vfalendysh/AuRA-1.3/STL/Spacer 12mm - 2x.stl

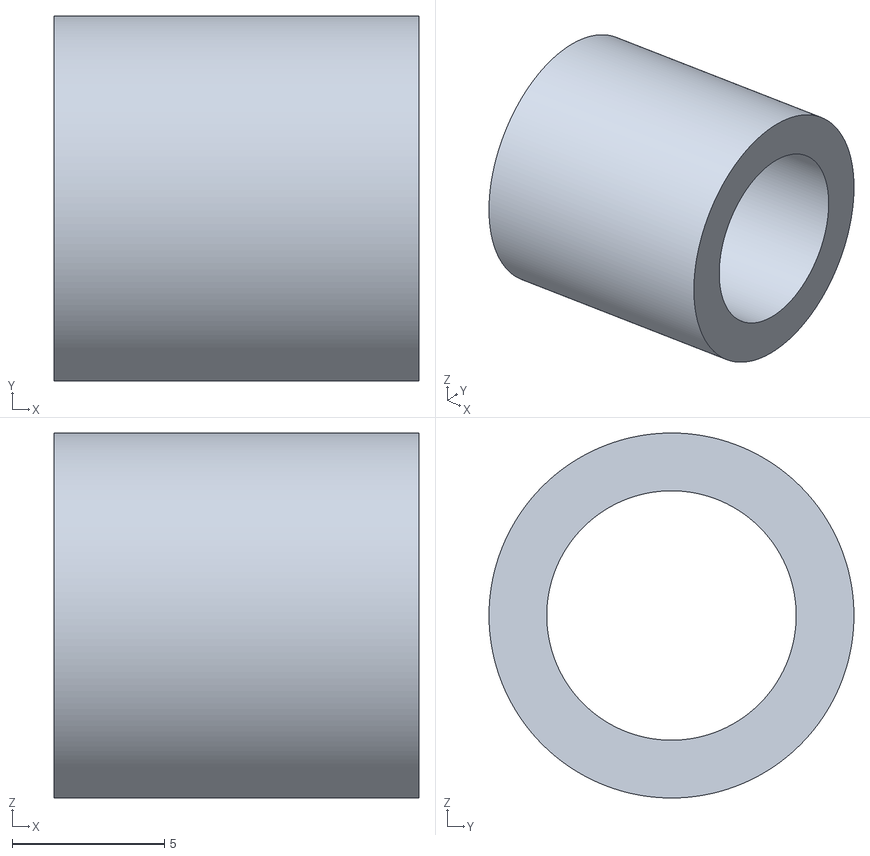
[picture p15: CAD file, 2024-05-07]
STL/Spacer 12mm - 2x.stl
12.0 x 12.0 x 12.0
