vfalendysh/AuRA-1.3/STL/Roller Jobo - 2x.stl

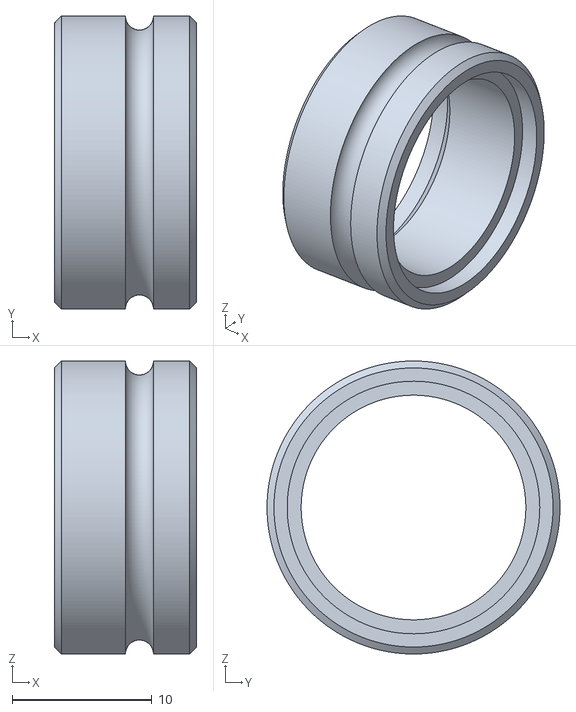
[picture p16: CAD file, 2024-05-07]
STL/Roller Jobo - 2x.stl
10.2 x 21.0 x 21.0
