vfalendysh/AuRA-1.3/STL/Spacer 08mm - 2x.stl

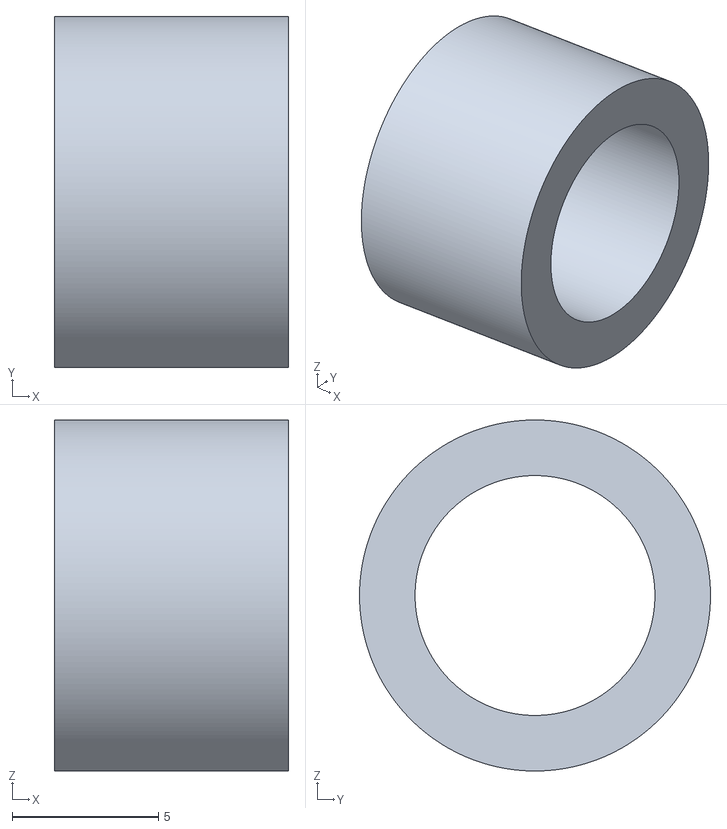
[picture p17: CAD file, 2024-05-07]
STL/Spacer 08mm - 2x.stl
8.00 x 12.0 x 12.0
