vfalendysh/AuRA-1.3/STL/Roller Flat - 6x.stl

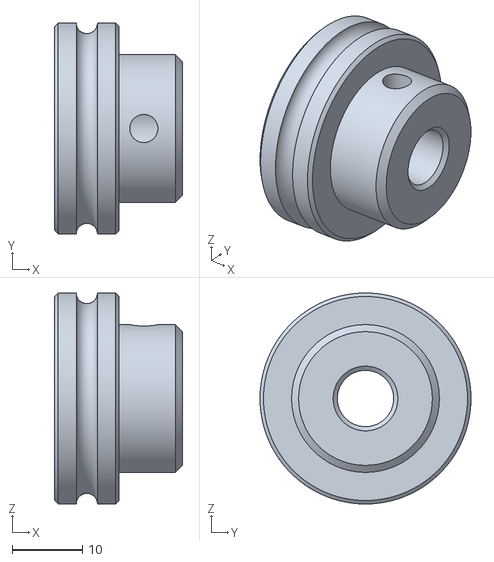
[picture p18: CAD file, 2024-05-07]
STL/Roller Flat - 6x.stl
18.2 x 30.0 x 30.0
